ansemjo/chronovfd/enclosure/frontmount/frontmount v0 (shell).png

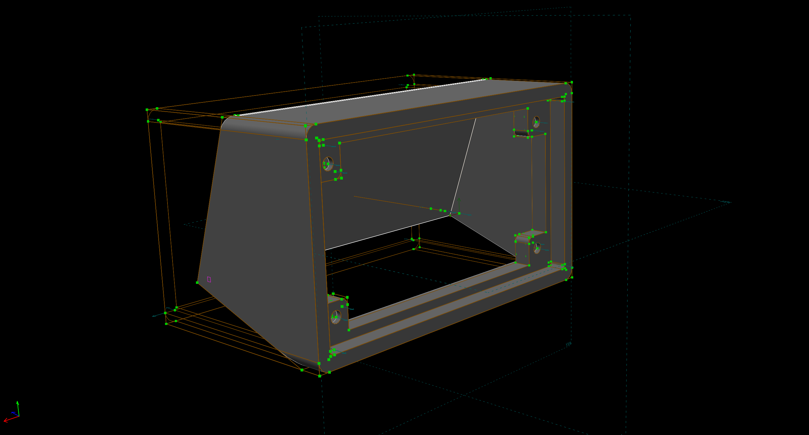
enclosure/frontmount/frontmount v0 (shell).png
