ansemjo/chronovfd/enclosure/frontmount/frontmount v1 (heat inserts).png

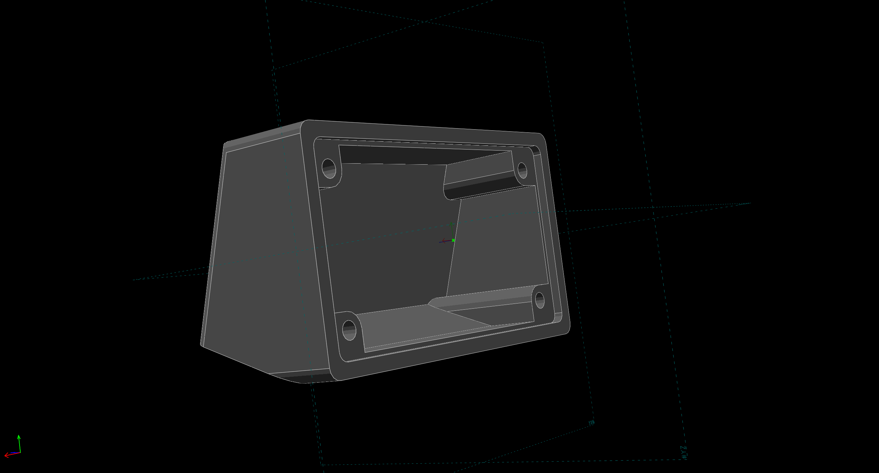
enclosure/frontmount/frontmount v1 (heat inserts).png
