ansemjo/chronovfd/enclosure/vfdshell/vfdshell_thinner_back.png

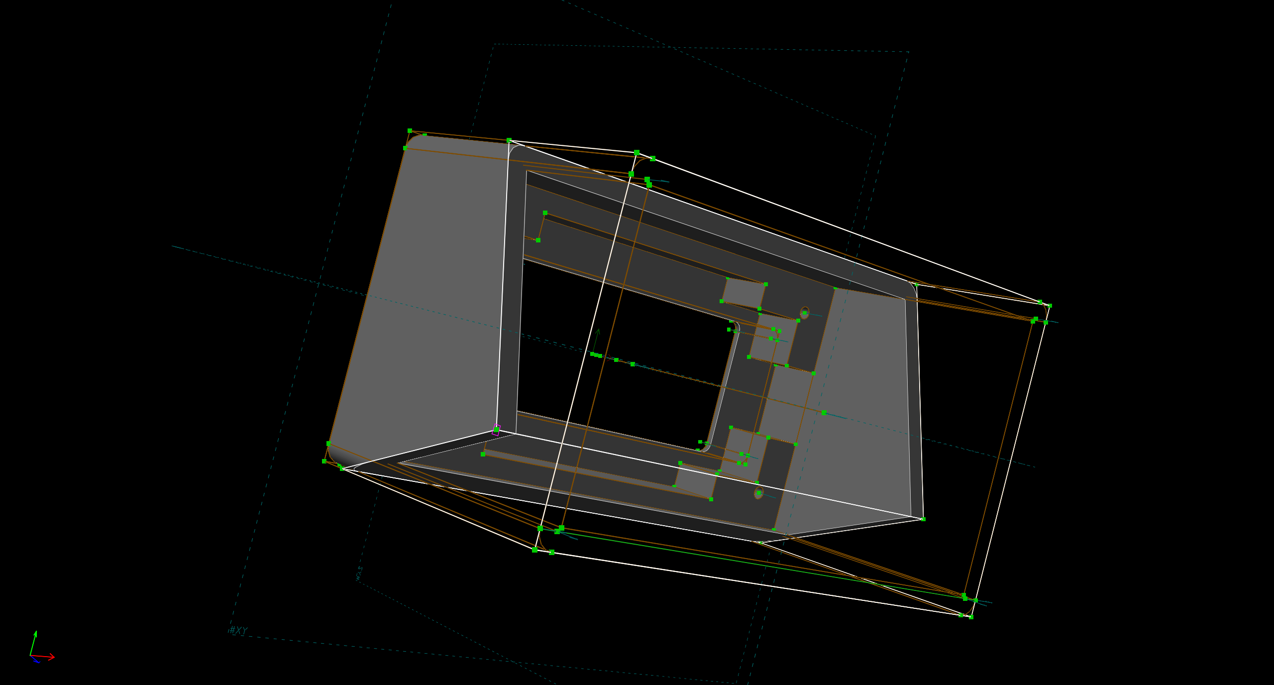
enclosure/vfdshell/vfdshell_thinner_back.png
