ansemjo/chronovfd/enclosure/vfdshell/vfdshell_thinner_front.png

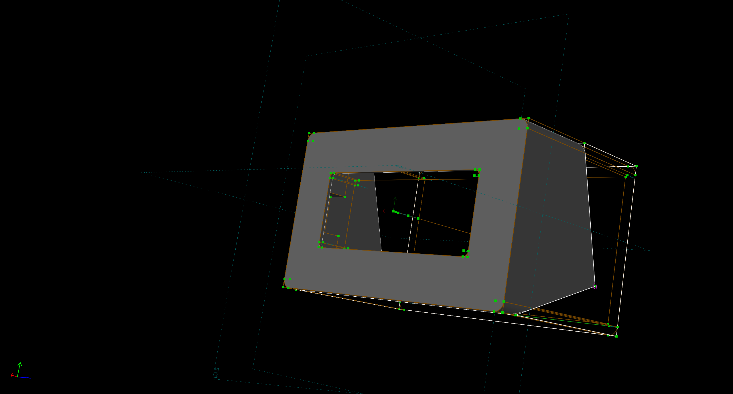
enclosure/vfdshell/vfdshell_thinner_front.png
