ansemjo/chronovfd/lcddriver/technoblogy-clock-firmware/PXL_20220921_120937253.jpg

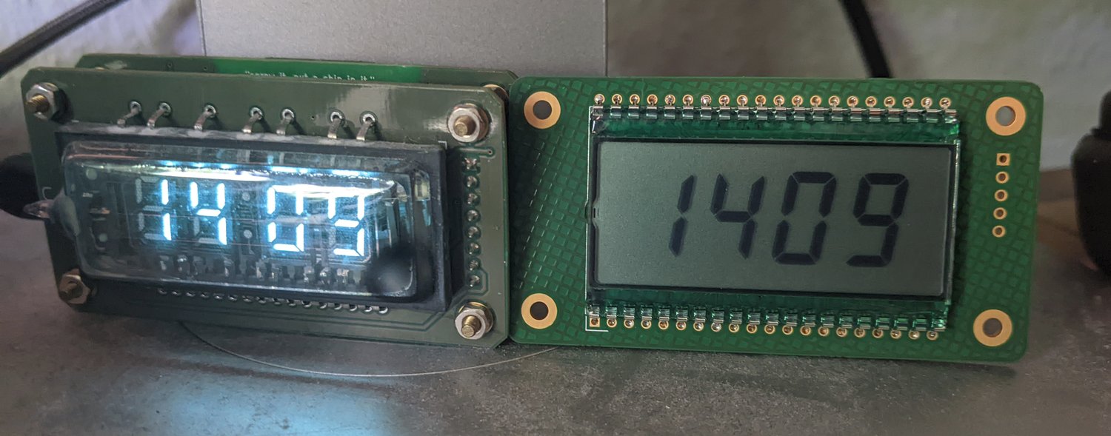
lcddriver/technoblogy-clock-firmware/PXL_20220921_120937253.jpg
