ansemjo/chronovfd/research/ivl2-7_5-datasheets/datasheet01.jpg

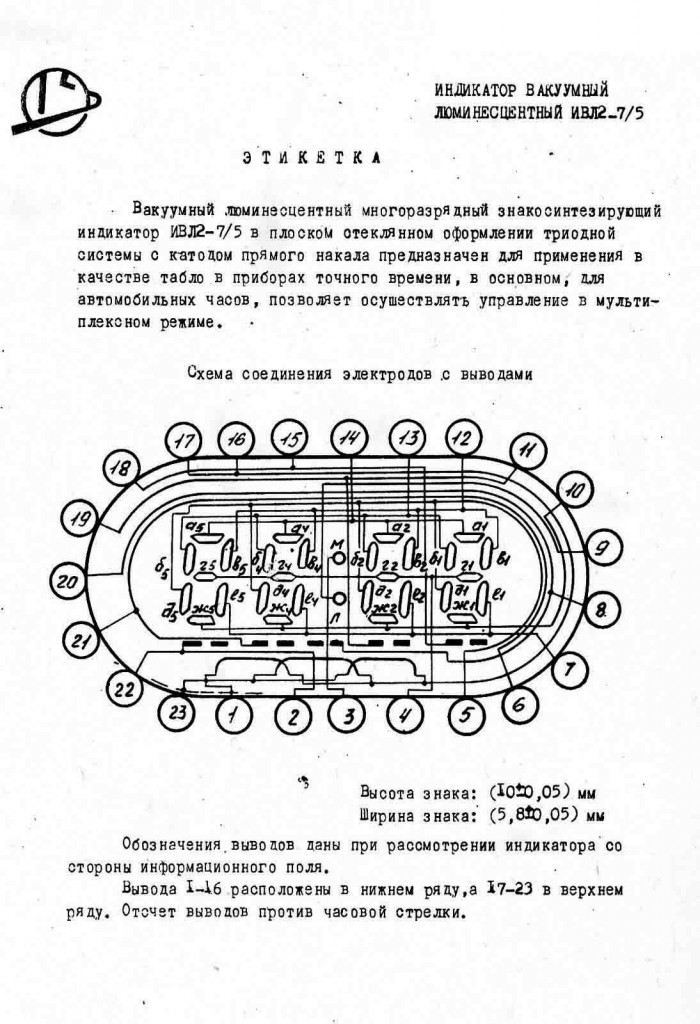
research/ivl2-7_5-datasheets/datasheet01.jpg
