ansemjo/chronovfd/research/ivl2-7_5-datasheets/datasheet02.jpg

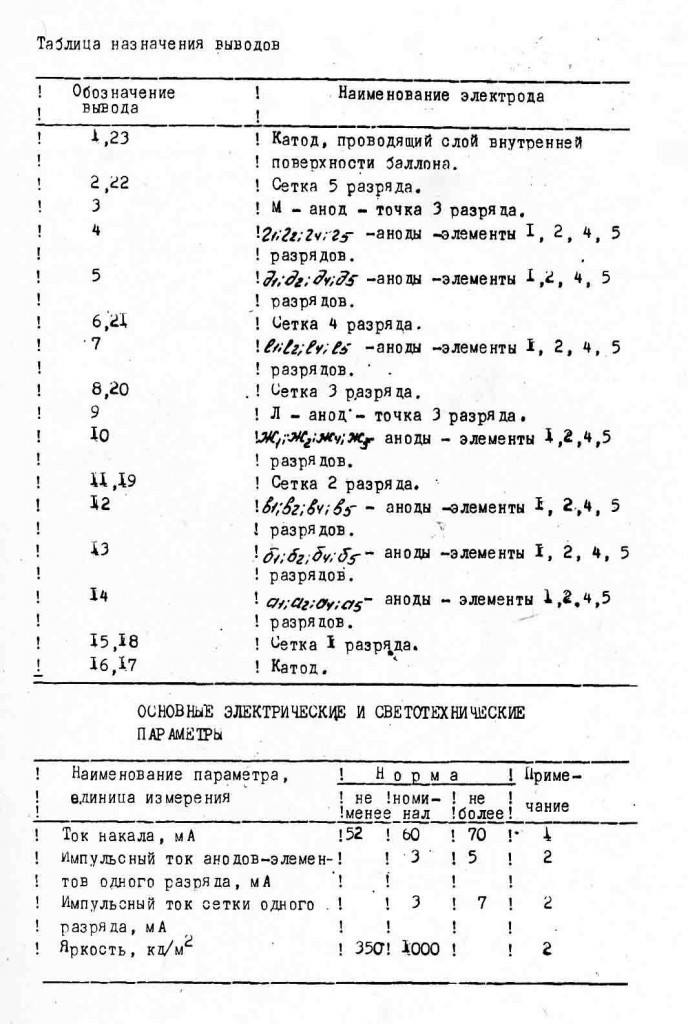
research/ivl2-7_5-datasheets/datasheet02.jpg
