ansemjo/chronovfd/research/ivl2-7_5-datasheets/dimensions.jpg

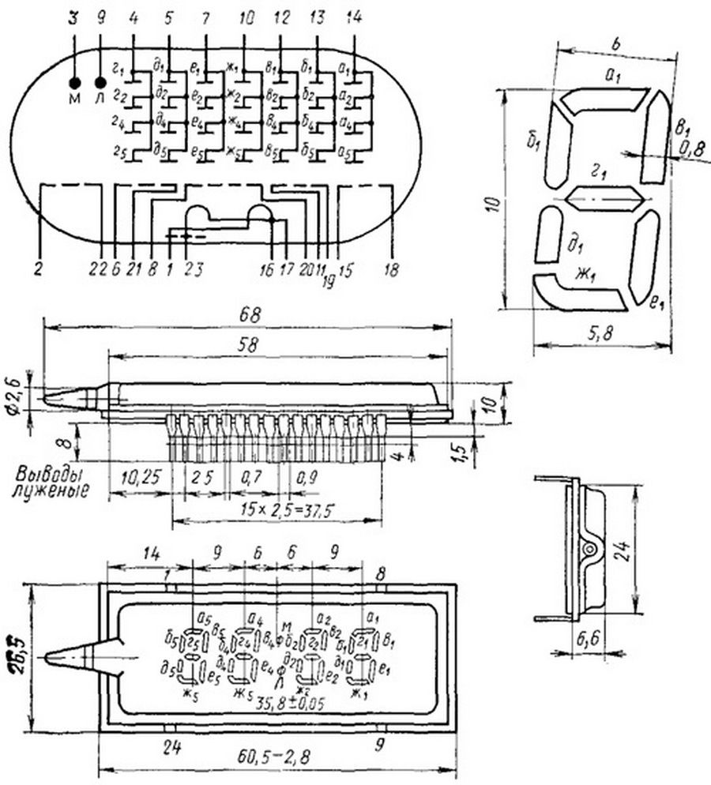
research/ivl2-7_5-datasheets/dimensions.jpg
