ansemjo/chronovfd/research/universal-vfd-psu/pcb_layout.jpg

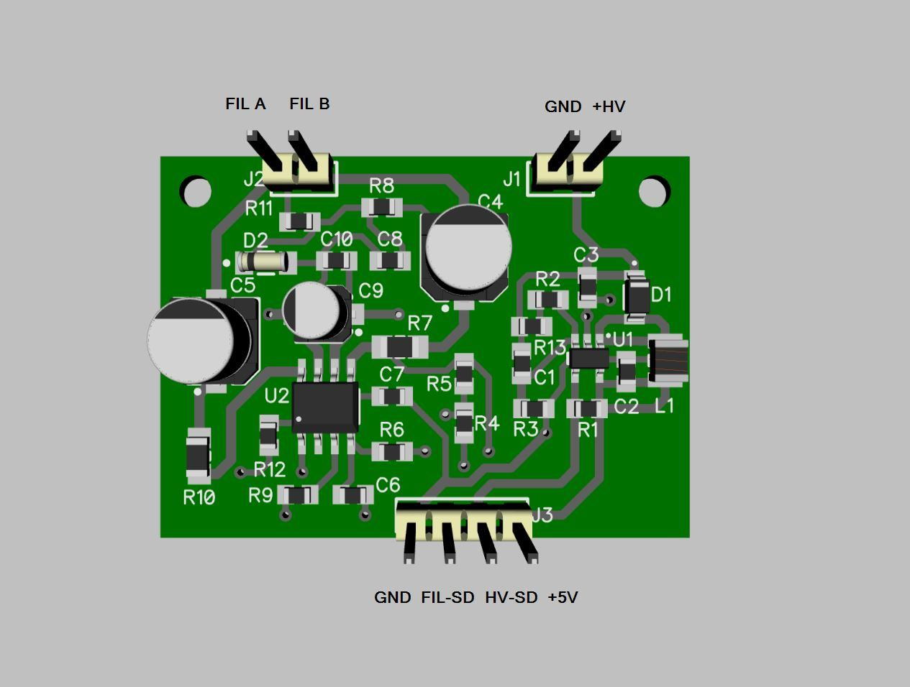
research/universal-vfd-psu/pcb_layout.jpg
