ansemjo/chronovfd/research/universal-vfd-psu/pcb_photo.jpg

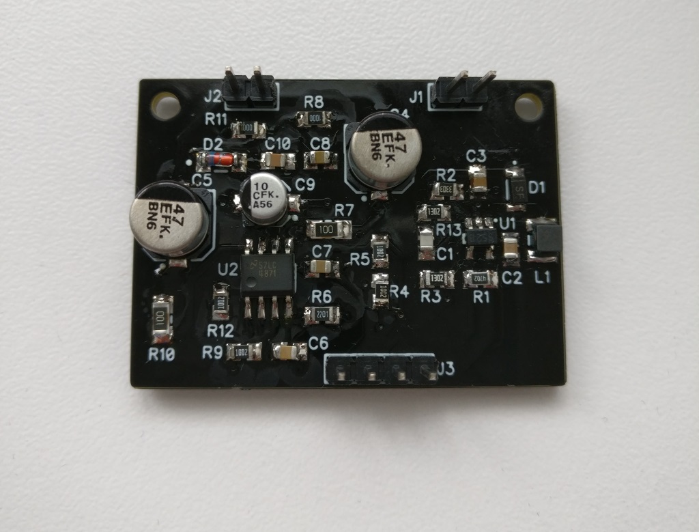
research/universal-vfd-psu/pcb_photo.jpg
