ansemjo/chronovfd/research/universal-vfd-psu/photos/filament_pwm_driver.jpg

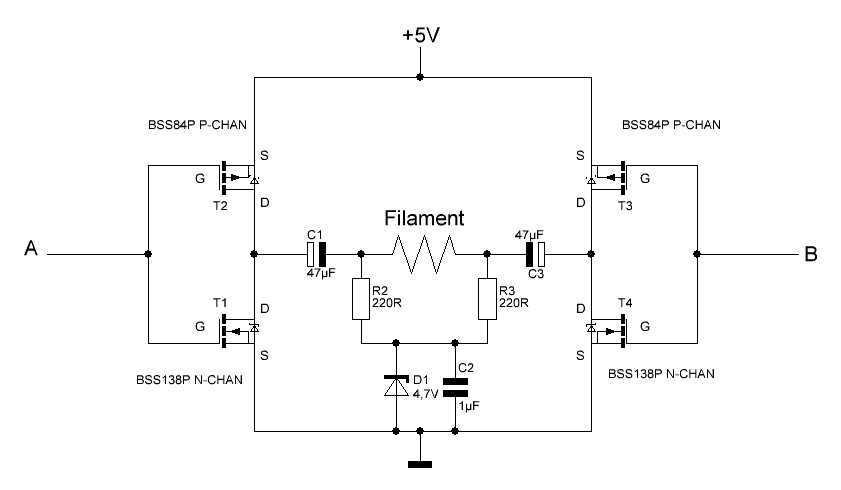
research/universal-vfd-psu/photos/filament_pwm_driver.jpg
