ansemjo/chronovfd/research/universal-vfd-psu/photos/img_20180704_203541__01.jpg

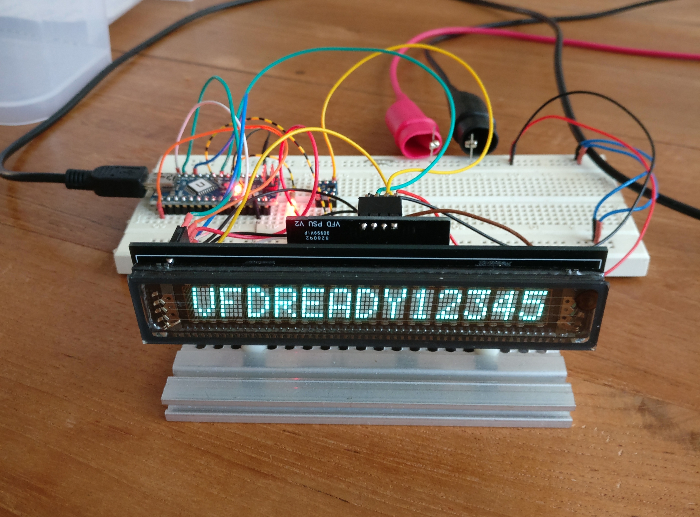
research/universal-vfd-psu/photos/img_20180704_203541__01.jpg
