ansemjo/chronovfd/research/universal-vfd-psu/photos/vfd_back.jpg

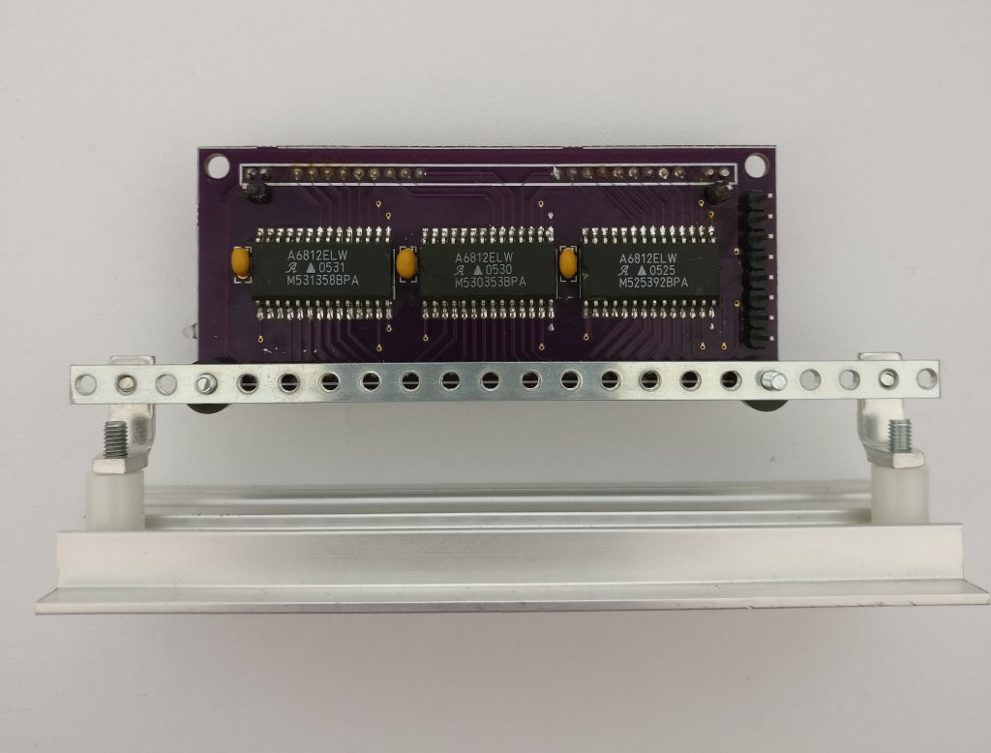
research/universal-vfd-psu/photos/vfd_back.jpg
