ansemjo/chronovfd/research/universal-vfd-psu/photos/vfd_front.jpg

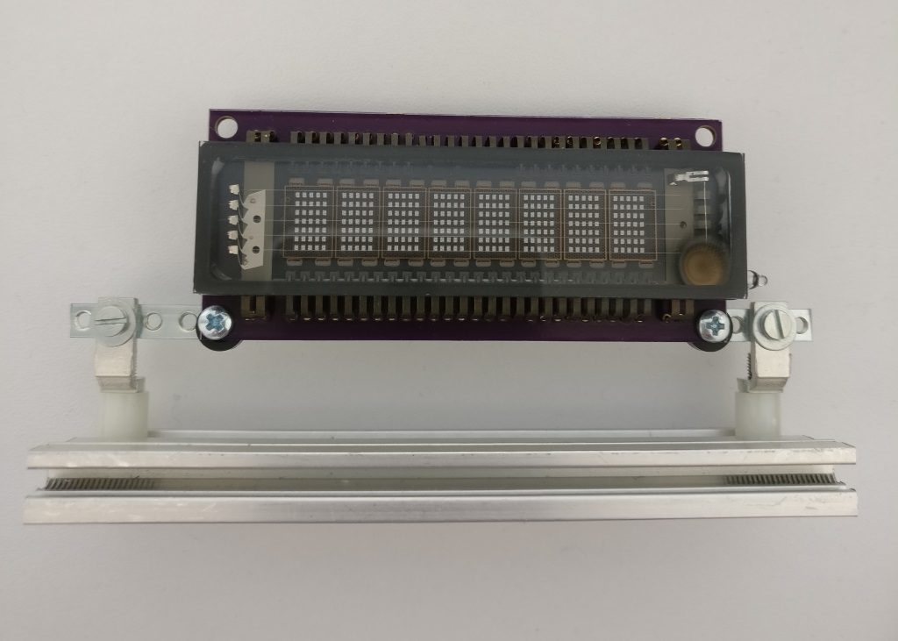
research/universal-vfd-psu/photos/vfd_front.jpg
