ansemjo/chronovfd/research/universal-vfd-psu/photos/vfd_on_frame.jpg

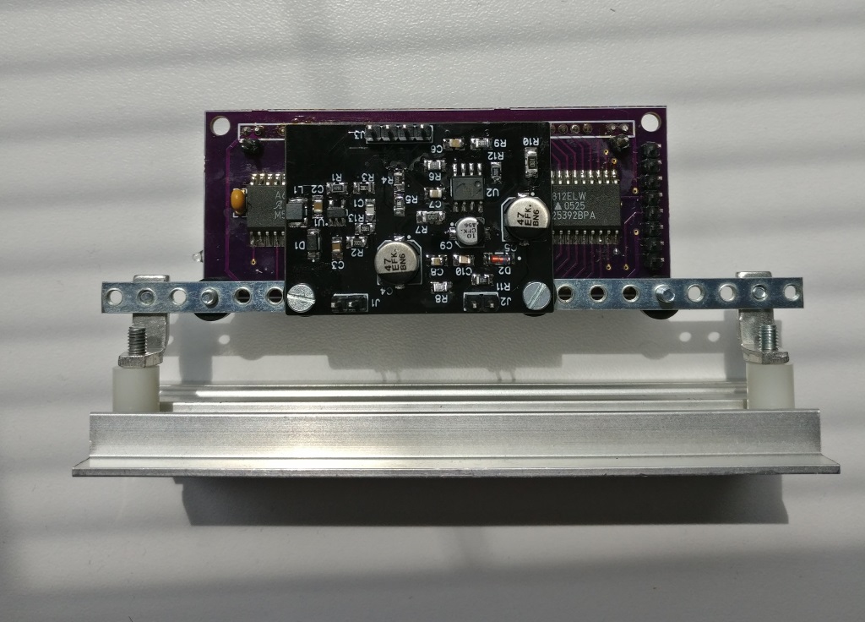
research/universal-vfd-psu/photos/vfd_on_frame.jpg
