ansemjo/chronovfd/research/universal-vfd-psu/photos/vfd_prototype.jpg

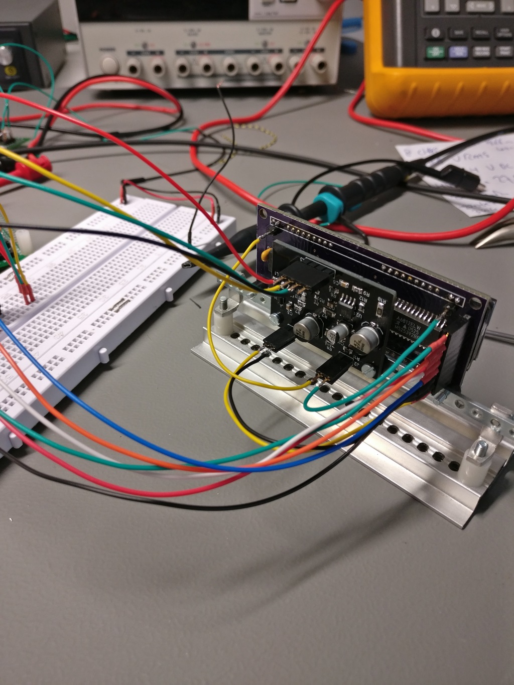
research/universal-vfd-psu/photos/vfd_prototype.jpg
