ansemjo/chronovfd/research/universal-vfd-psu/resistor_values.jpg

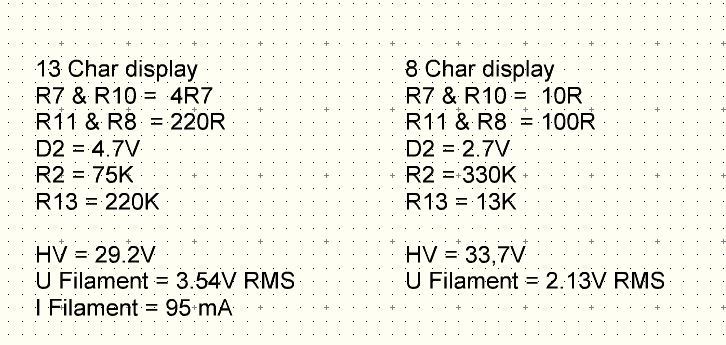
research/universal-vfd-psu/resistor_values.jpg
