ansemjo/chronovfd/vfddriver/render-back.png

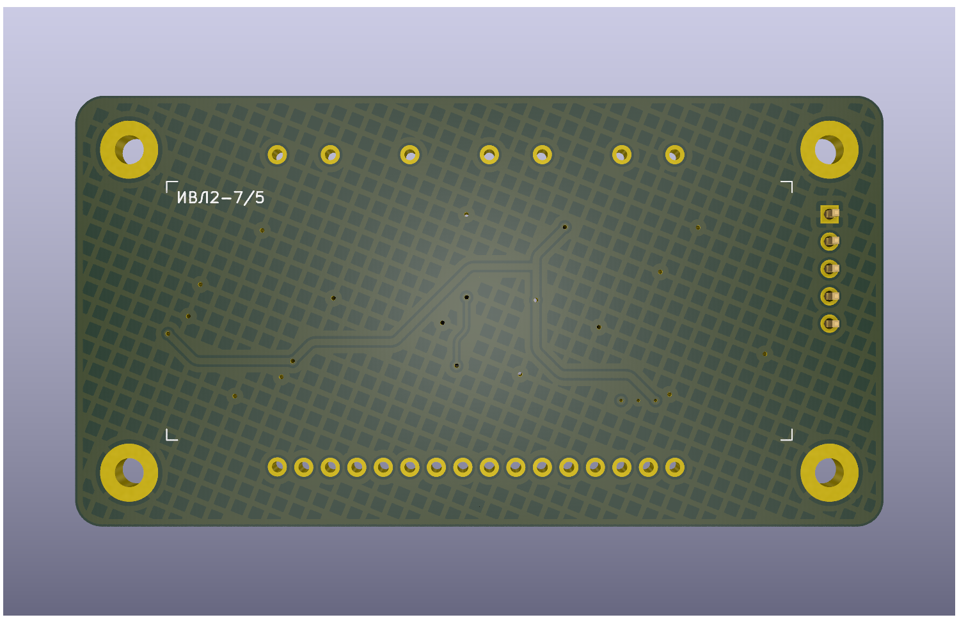
vfddriver/render-back.png
