ansemjo/chronovfd/vfddriver/vfddriver-back.png

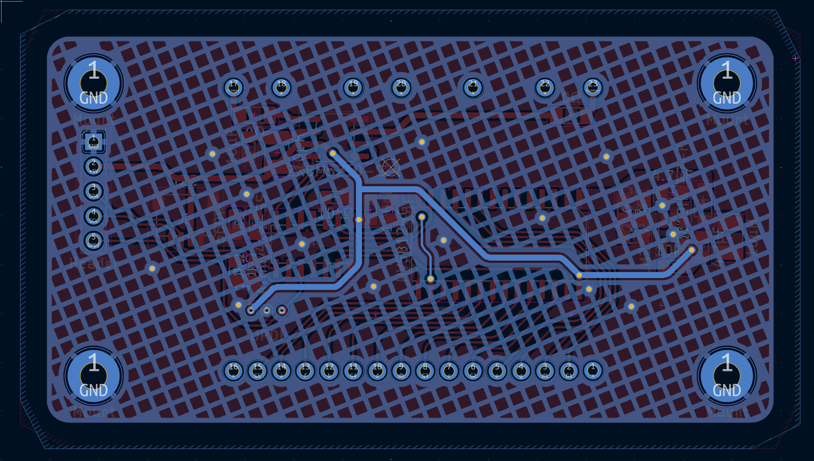
vfddriver/vfddriver-back.png
