ansemjo/chronovfd/vfddriver/vfddriver-front.png

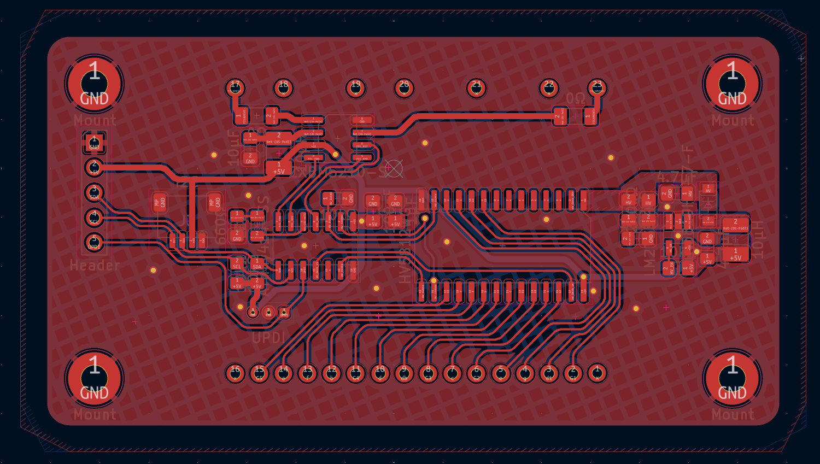
vfddriver/vfddriver-front.png
