ansemjo/chronovfd/experiments/breadboard_psu/breadboard_psu.jpg

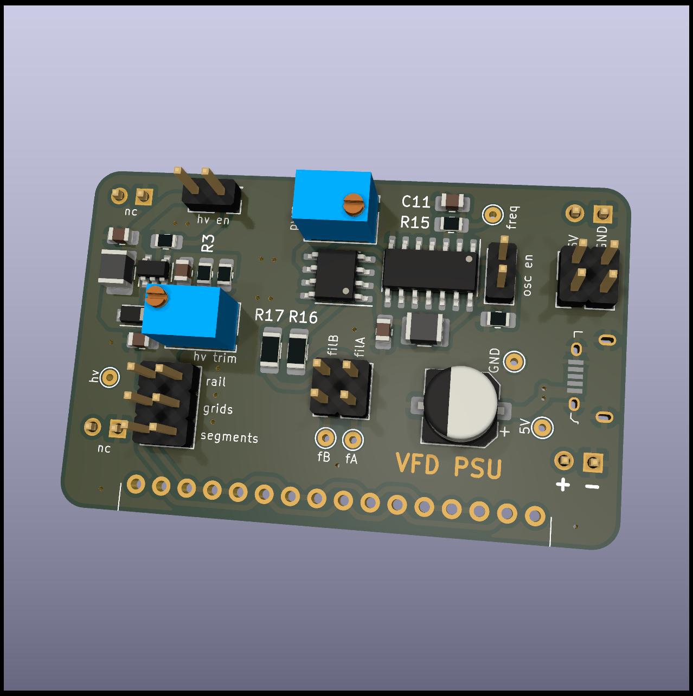
experiments/breadboard_psu/breadboard_psu.jpg
