ansemjo/chronovfd/research/universal-vfd-psu/photos/filament_freq_measurement.jpg

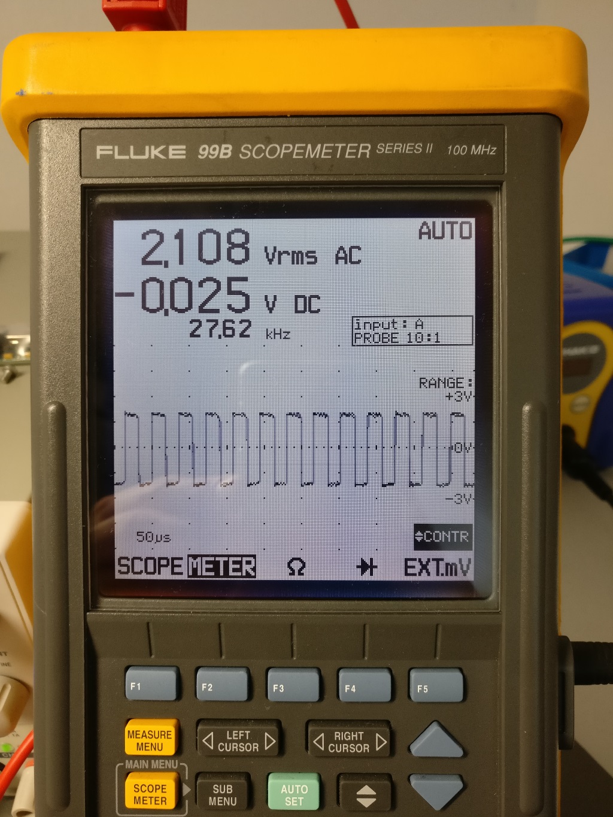
research/universal-vfd-psu/photos/filament_freq_measurement.jpg
