ansemjo/chronovfd/sandwich/firmware/src/realtimeclock.h

// Copyright (c) 2020 Anton Semjonov
// Licensed under the MIT License

#pragma once

#include <esp_err.h>
#include "i2cdev.h"

#define I2C_SDA 21
#define I2C_SCL 22
#define RTC_MODEL "Maxim DS1338"

// battery-backed ds13xx i2c rtc
void realtimeclock_init(gpio_num_t sda, gpio_num_t scl);
time_t realtimeclock_read_from_rtc();
void realtimeclock_update_rtc();
void realtimeclock_update_rtc_fixedtime(const char *timestamp);
time_t realtimeclock_get_lastsync();
void realtimeclock_set_lastsync(time_t t);

// tasks
void clockface_task(void *arg);
void clockface(TaskHandle_t *task);

// internet time synchronization
const char* sntp_servers[2];
esp_err_t sntp_sync(TickType_t timeout);
void sntp_sync_schedule(void *arg);
